jsbursik/Janus-Keyboard/output/outlines/_insert_holes.dxf

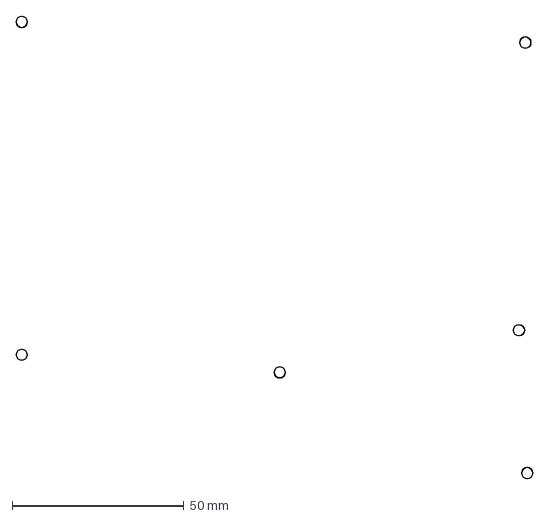
[picture p15: CAD file, 2026-09-18]
output/outlines/_insert_holes.dxf
150.7 x 134.8 mm
