jsbursik/Janus-Keyboard/output/outlines/inserts.dxf

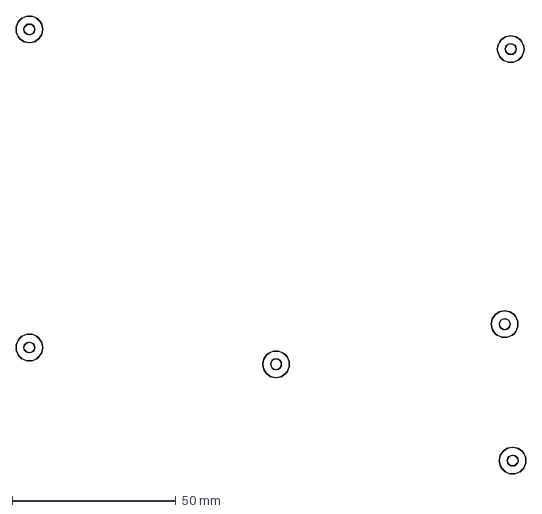
[picture p16: CAD file, 2024-06-29]
output/outlines/inserts.dxf
155.5 x 139.6 mm
