jsbursik/Janus-Keyboard/output/outlines/keyplate.dxf

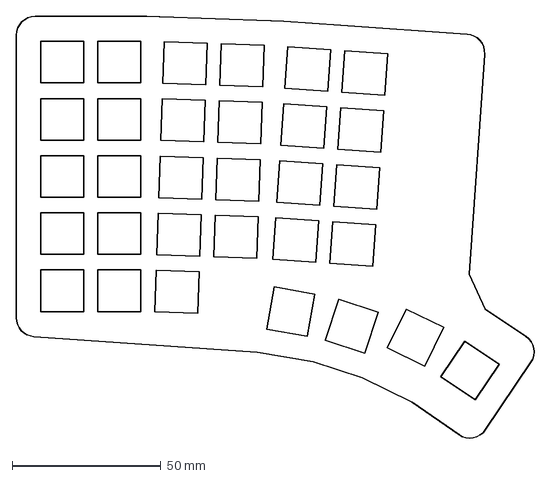
[picture p17: CAD file, 2024-06-23]
output/outlines/keyplate.dxf
174.8 x 141.9 mm
