jsbursik/Janus-Keyboard/output/outlines/drilled_board.dxf

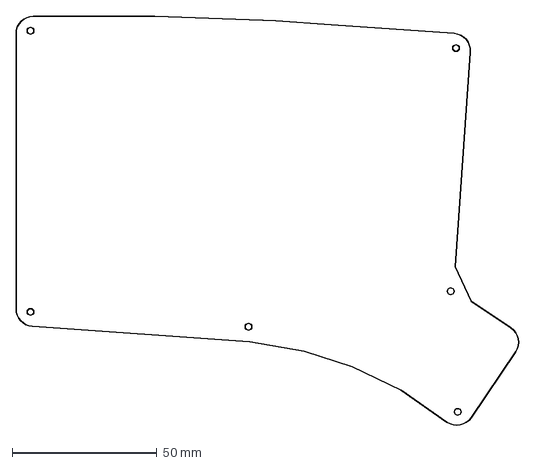
[picture p18: CAD file, 2024-06-23]
output/outlines/drilled_board.dxf
174.2 x 141.3 mm
