jsbursik/Janus-Keyboard/output/outlines/keyplate_drilled.dxf

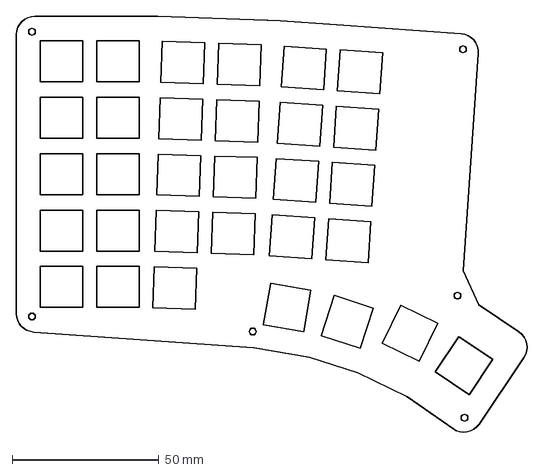
[picture p19: CAD file, 2024-06-23]
output/outlines/keyplate_drilled.dxf
174.8 x 141.9 mm
