jsbursik/Janus-Keyboard/output/outlines/standoffs.dxf

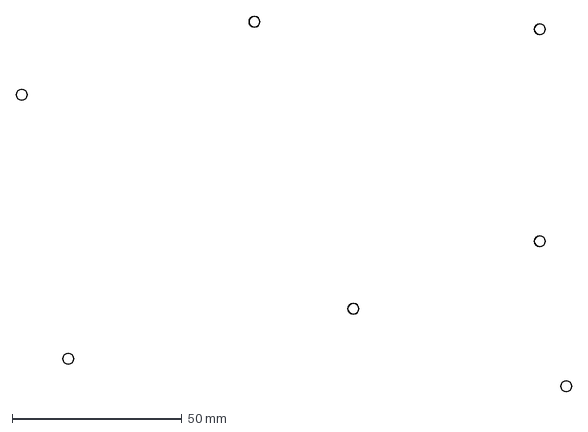
[picture p20: CAD file, 2024-05-17]
output/outlines/standoffs.dxf
163.7 x 110.6 mm
