jsbursik/Janus-Keyboard/output/outlines/holes.dxf

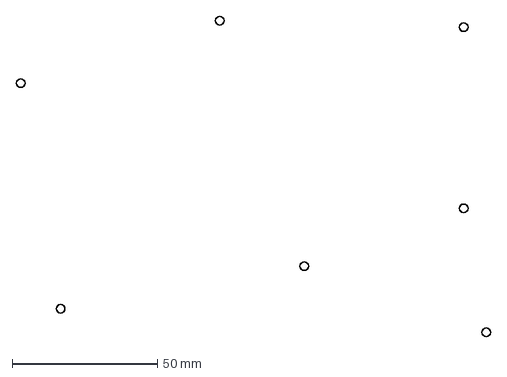
[picture p21: CAD file, 2024-05-15]
output/outlines/holes.dxf
163.5 x 110.4 mm
