jsbursik/Janus-Keyboard/output/outlines/combo.dxf

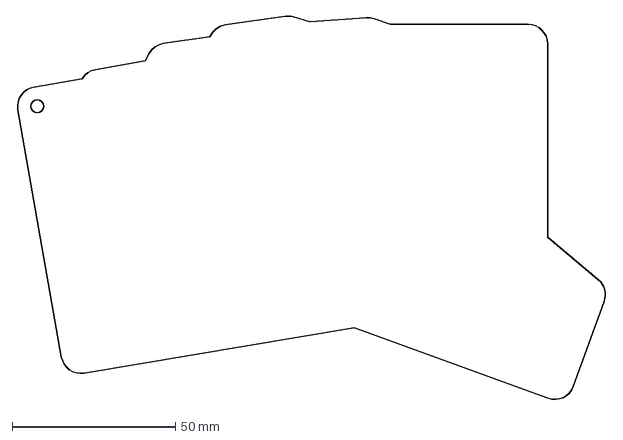
[picture p22: CAD file, 2024-05-15]
output/outlines/combo.dxf
181.2 x 117.7 mm
