jsbursik/Janus-Keyboard/output/outlines/wall.yaml

models:
    export:
        models:
            a:
                models:
                    a:
                        models: {}
                        origin:
                            - 0
                            - 0
                    b:
                        models:
                            '0':
                                paths:
                                    p1_Top_Top_Top:
                                        type: line
                                        origin:
                                            - 32.6
                                            - -159.1
                                        end:
                                            - 32.6
                                            - -64.1
                                    p1_EndCap_Outer_Outer:
                                        type: arc
                                        origin:
                                            - 40.9
                                            - -64.1
                                        radius: 8.3
                                        startAngle: 90
                                        endAngle: 180
                                    p2_Top_Top_Top:
                                        type: line
                                        origin:
                                            - 40.9
                                            - -55.80000000000001
                                        end:
                                            - 78.3
                                            - -55.80000000000001
                                    p4_EndCap_Outer_Outer:
                                        type: arc
                                        origin:
                                            - 78.3
                                            - -64.10000000000001
                                        radius: 8.3
                                        startAngle: 88.8450499018668
                                        endAngle: 90
                                    p5_Top_Top_Top:
                                        type: line
                                        origin:
                                            - 78.46729739999999
                                            - -55.801686200000006
                                        end:
                                            - 82.6707075
                                            - -55.8864287
                                    p5_EndCap_Outer_Outer:
                                        type: arc
                                        origin:
                                            - 82.5034101
                                            - -64.18474250000001
                                        radius: 8.3
                                        startAngle: 87.999999823808
                                        endAngle: 88.8450496552912
                                    p6_Top_Top_Top:
                                        type: line
                                        origin:
                                            - 82.79307590000002
                                            - -55.88979860000001
                                        end:
                                            - 120.17029280000001
                                            - -57.19503970000002
                                    p8_EndCap_Outer_Outer:
                                        type: arc
                                        origin:
                                            - 119.88062700000002
                                            - -65.4899836
                                        radius: 8.3
                                        startAngle: 86.8450496094199
                                        endAngle: 88.0000001201171
                                    p9_Top_Top_Top:
                                        type: line
                                        origin:
                                            - 120.33742950000003
                                            - -57.20256350000001
                                        end:
                                            - 124.53532190000003
                                            - -57.43395130000001
                                    p9_EndCap_Outer_Outer:
                                        type: arc
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
                        origin:
                            - 0
                            - 0
                origin:
                    - 0
                    - 0
        origin:
            - 0
            - 0
units: mm
origin:
    - 0
    - 0
